zschunky/magicFlash64/pics/469-timing.png

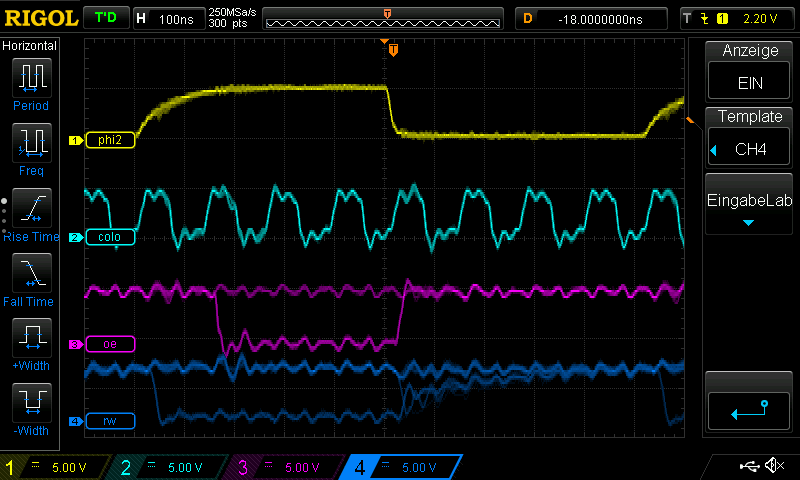
pics/469-timing.png
