zschunky/magicFlash64/pics/P_20190113_054123.jpg

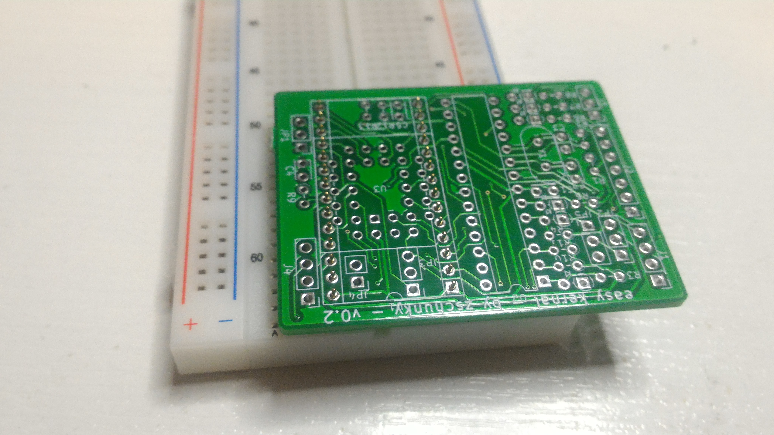
pics/P_20190113_054123.jpg
