zschunky/magicFlash64/pics/P_20190113_054204.jpg

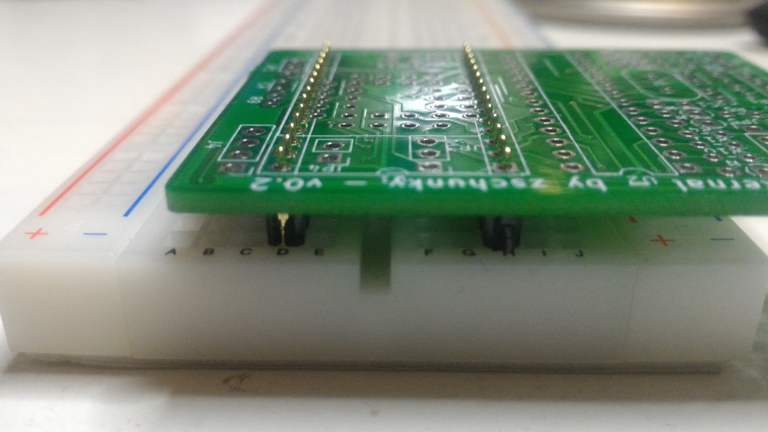
pics/P_20190113_054204.jpg
