zschunky/magicFlash64/pics/P_20190113_054526.jpg

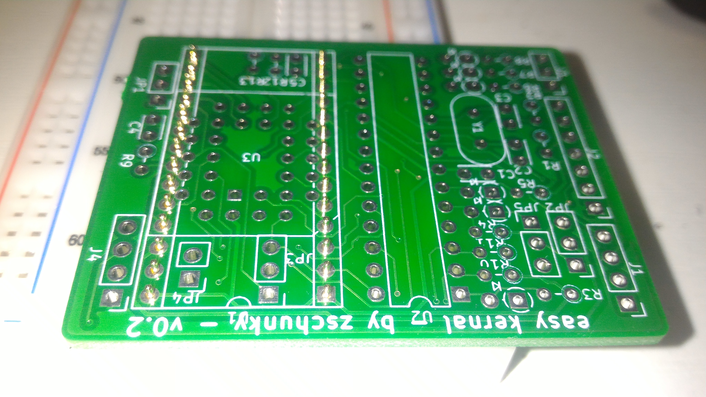
pics/P_20190113_054526.jpg
