zschunky/magicFlash64/pics/P_20190113_054540.jpg

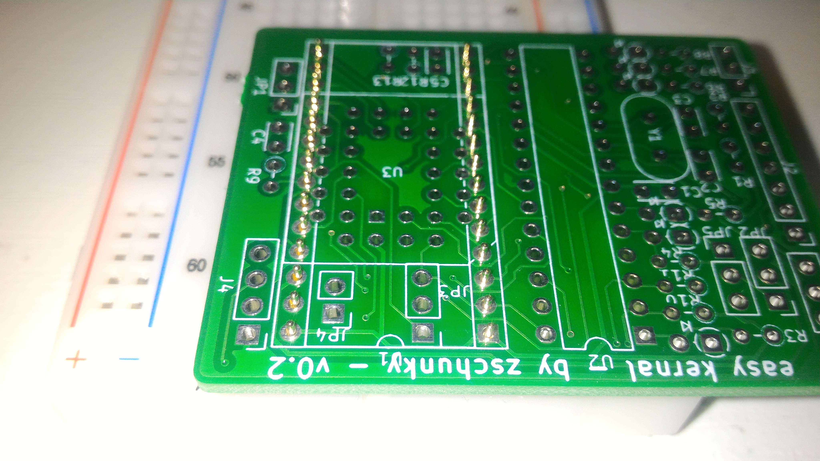
pics/P_20190113_054540.jpg
