zschunky/magicFlash64/pics/P_20190113_054853.jpg

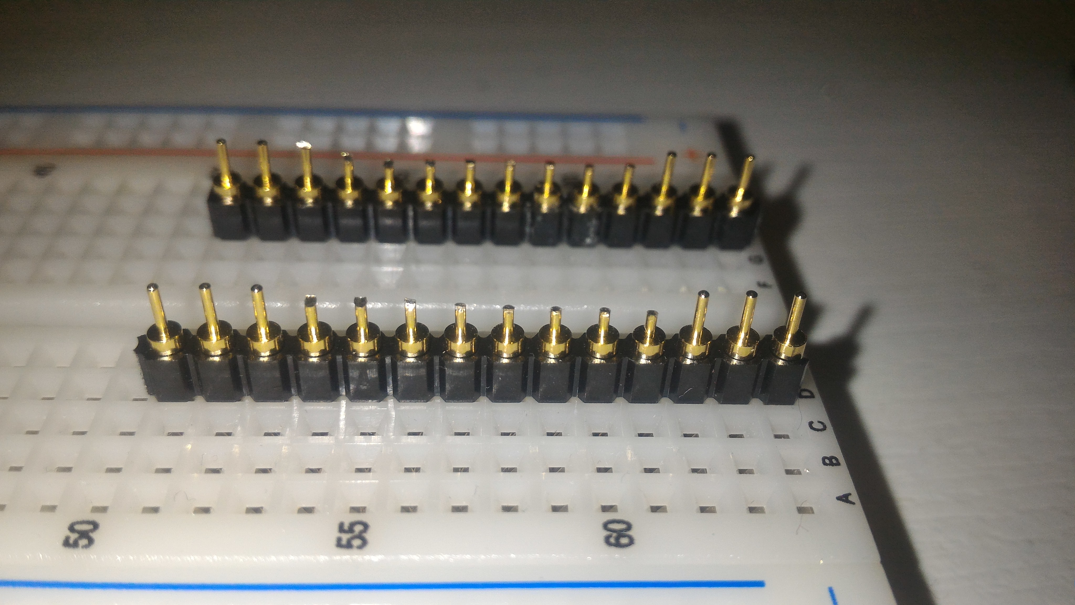
pics/P_20190113_054853.jpg
