zschunky/magicFlash64/pics/P_20190113_055543.jpg

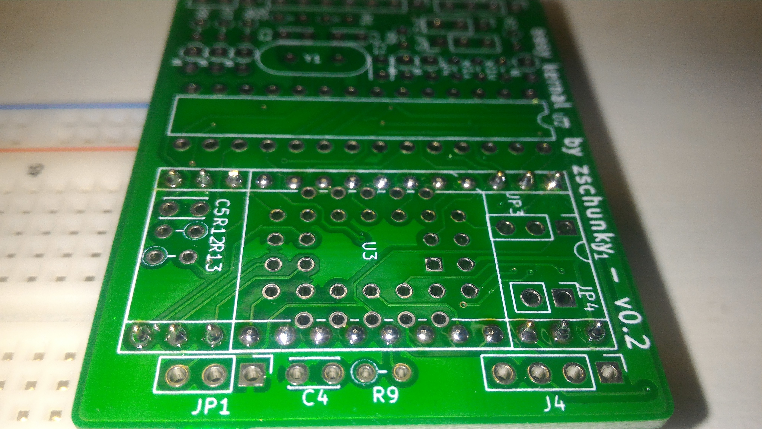
pics/P_20190113_055543.jpg
