zschunky/magicFlash64/pics/P_20190113_055739.jpg

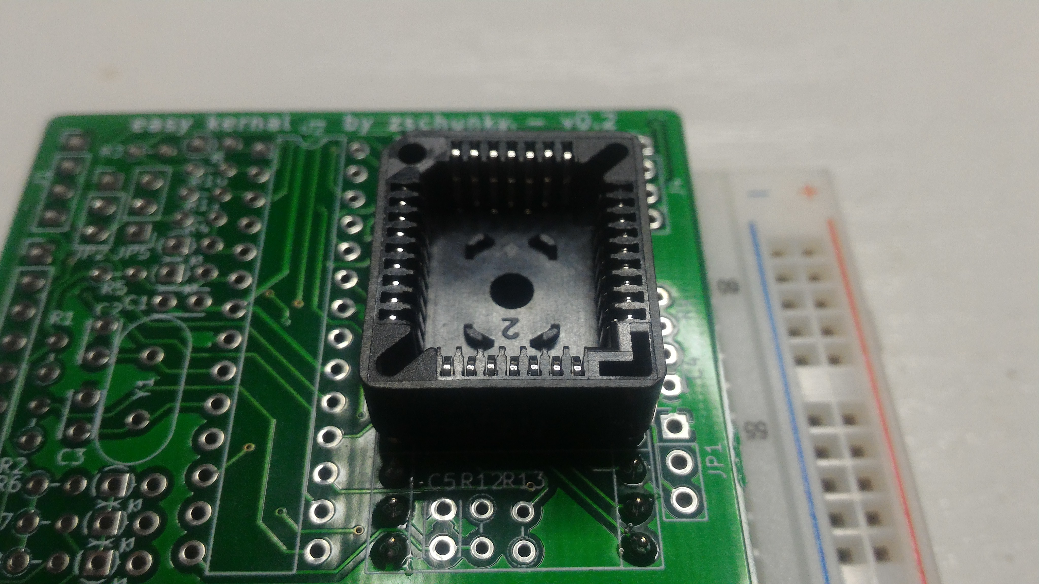
pics/P_20190113_055739.jpg
