zschunky/magicFlash64/pics/P_20190113_055753.jpg

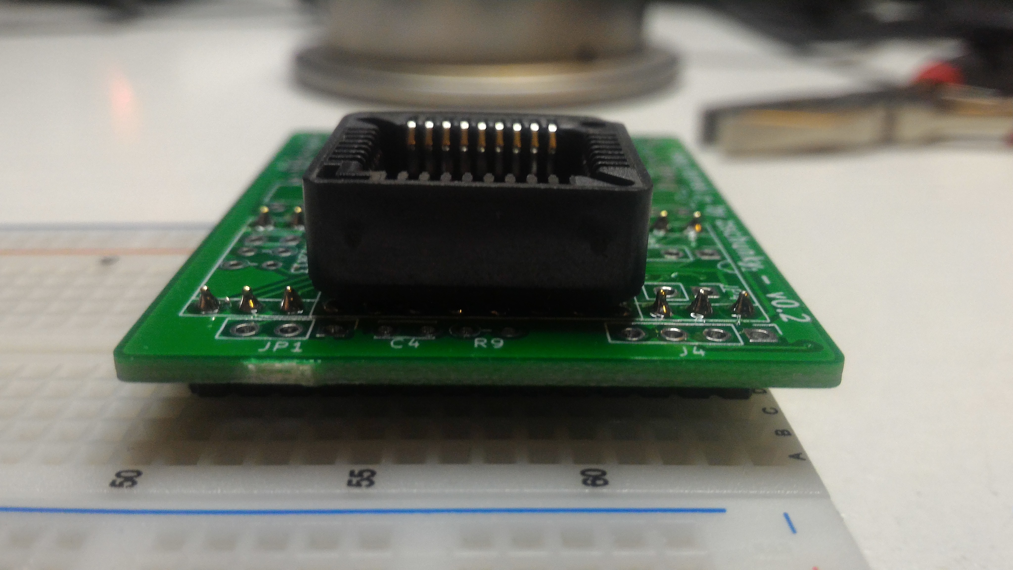
pics/P_20190113_055753.jpg
