zschunky/magicFlash64/pics/P_20190113_060007.jpg

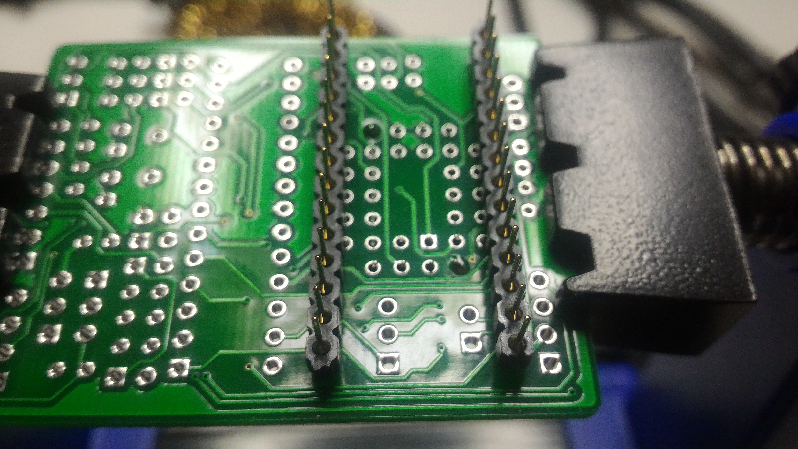
pics/P_20190113_060007.jpg
