zschunky/magicFlash64/pics/P_20190113_060031.jpg

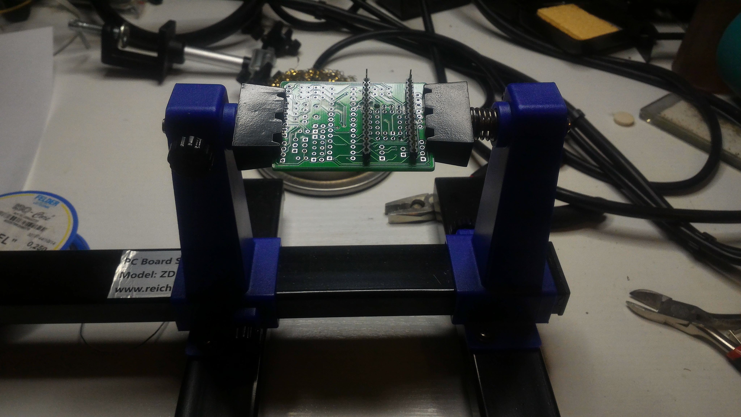
pics/P_20190113_060031.jpg
