zschunky/magicFlash64/pics/P_20190113_060040.jpg

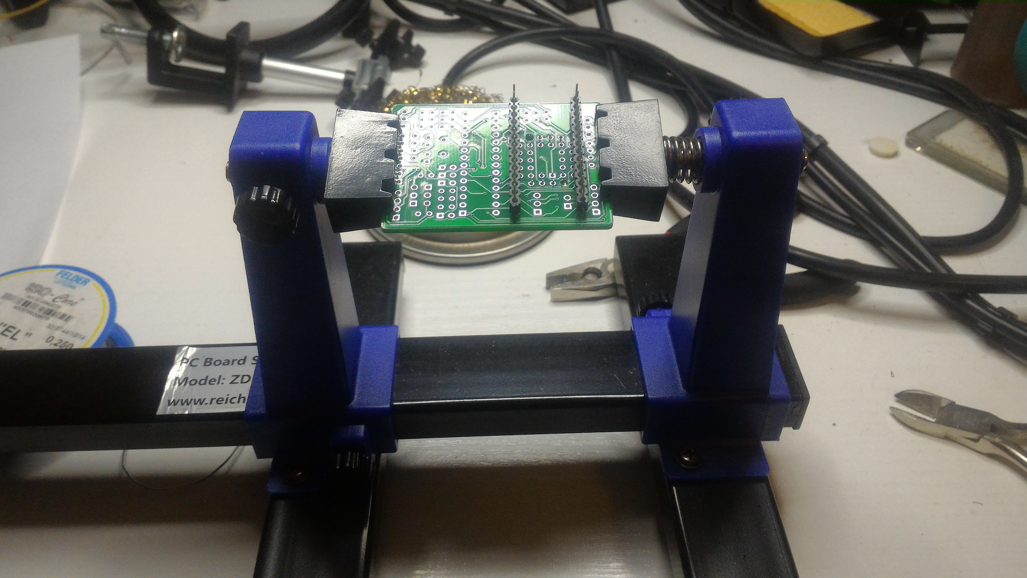
pics/P_20190113_060040.jpg
