zschunky/magicFlash64/pics/P_20190113_060500.jpg

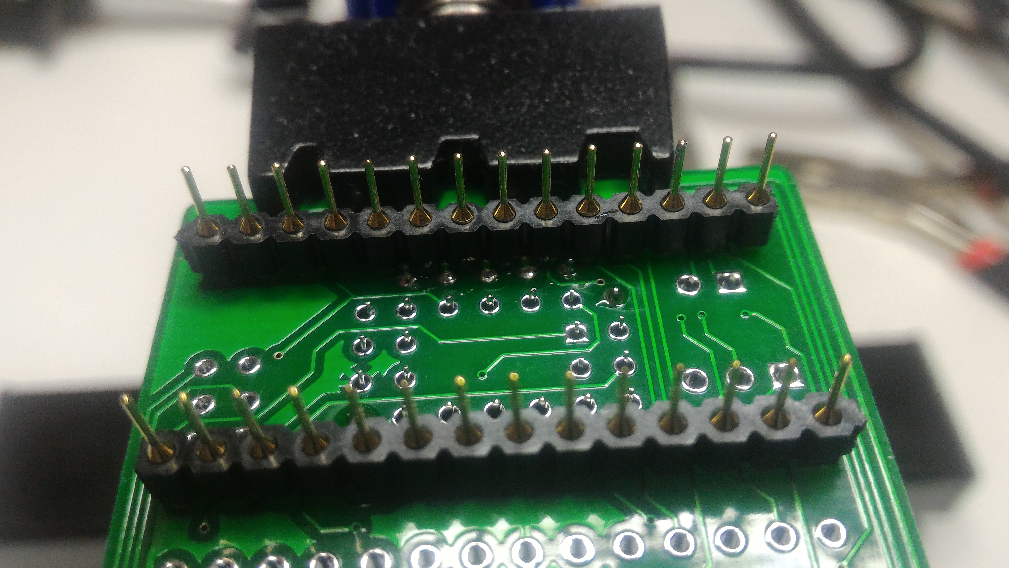
pics/P_20190113_060500.jpg
