zschunky/magicFlash64/pics/P_20190113_060512.jpg

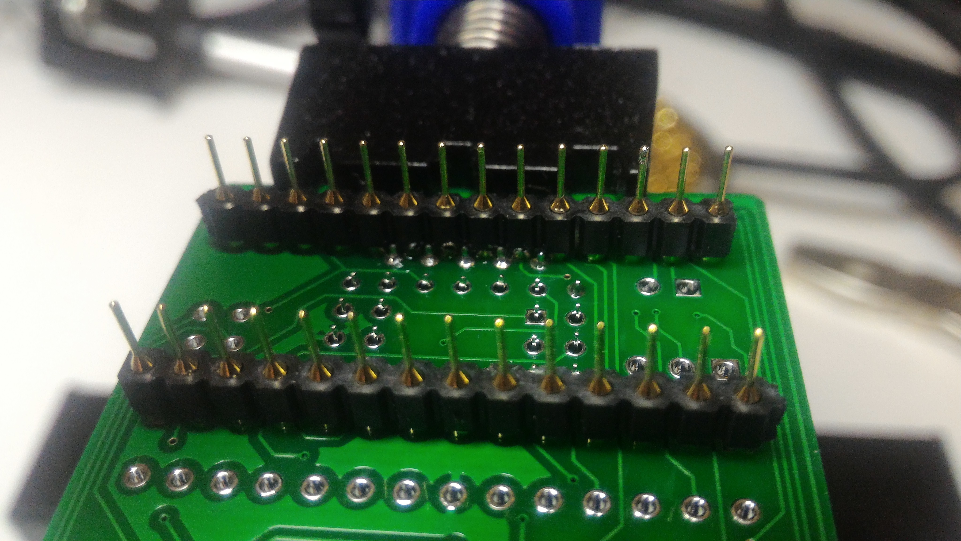
pics/P_20190113_060512.jpg
