zschunky/magicFlash64/pics/P_20190113_075411.jpg

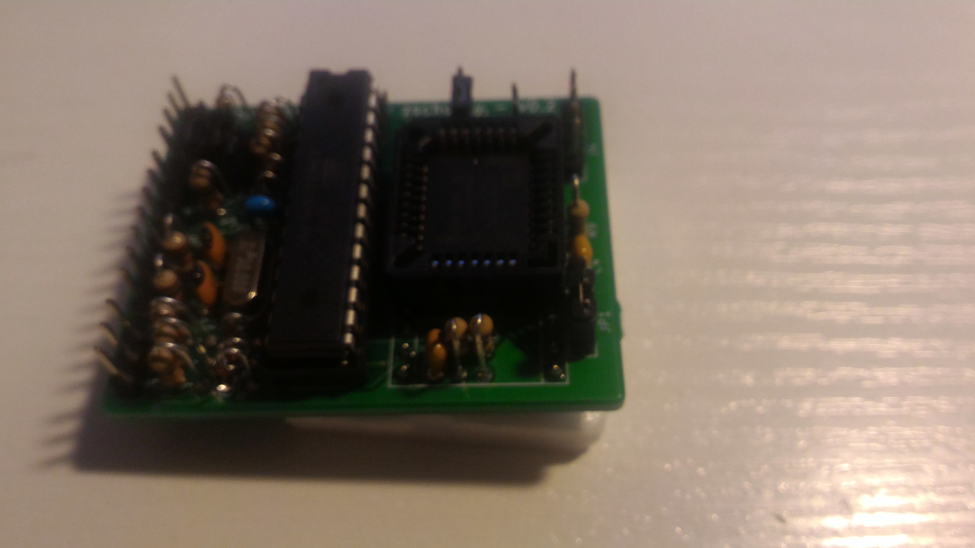
pics/P_20190113_075411.jpg
