zschunky/magicFlash64/pics/P_20190113_075420.jpg

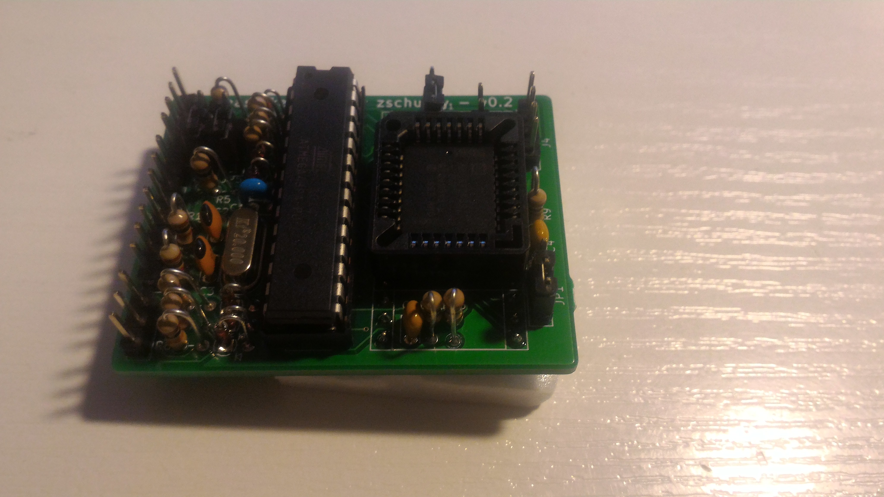
pics/P_20190113_075420.jpg
