zschunky/magicFlash64/pics/P_20190113_075424.jpg

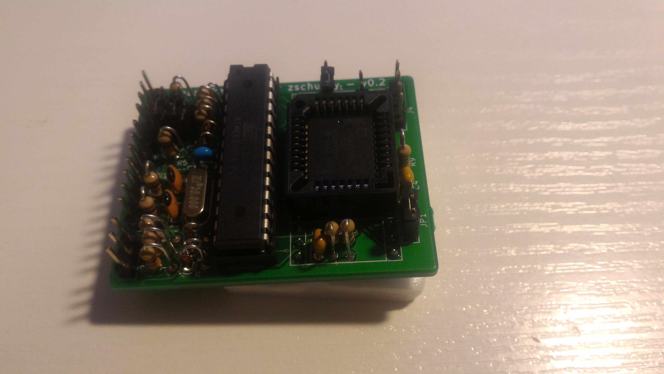
pics/P_20190113_075424.jpg
