zschunky/magicFlash64/pics/P_20190113_075440.jpg

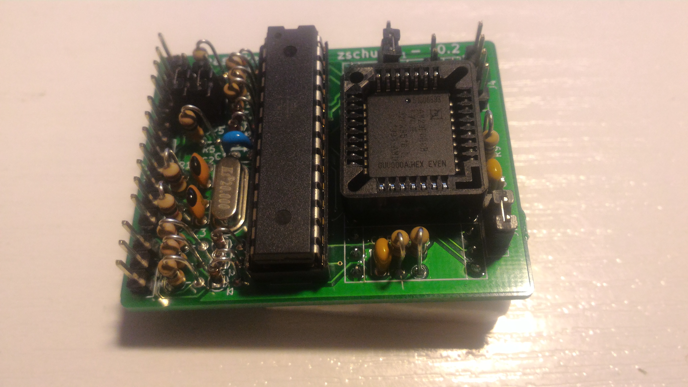
pics/P_20190113_075440.jpg
