zschunky/magicFlash64/pics/P_20190203_124354.jpg

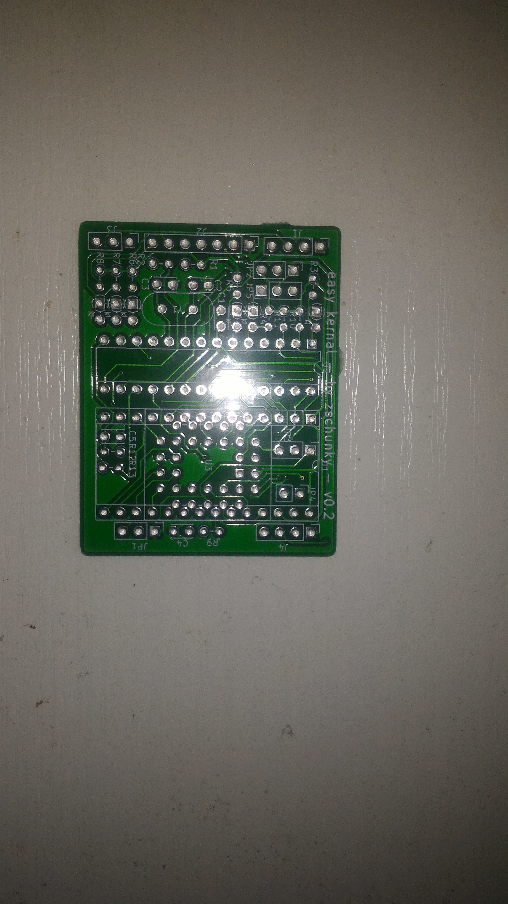
pics/P_20190203_124354.jpg
