zschunky/magicFlash64/pics/P_20190203_193504.jpg

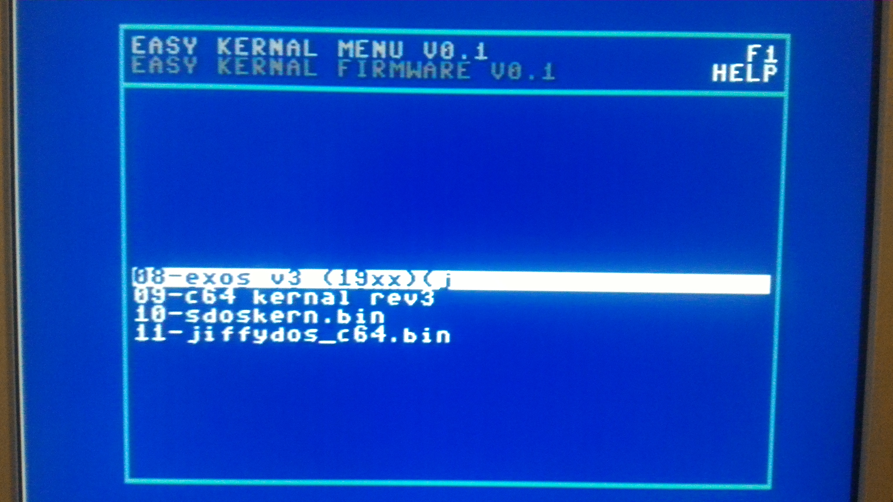
pics/P_20190203_193504.jpg
