zschunky/magicFlash64/pics/P_20190203_193543.jpg

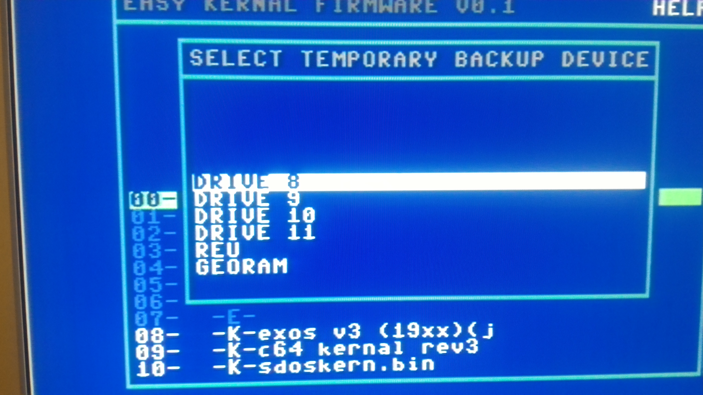
pics/P_20190203_193543.jpg
