zschunky/magicFlash64/pics/P_20190203_193612.jpg

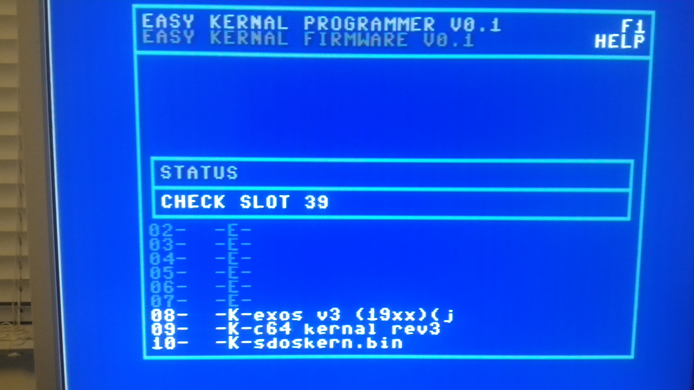
pics/P_20190203_193612.jpg
