zschunky/magicFlash64/pics/P_20190203_193618.jpg

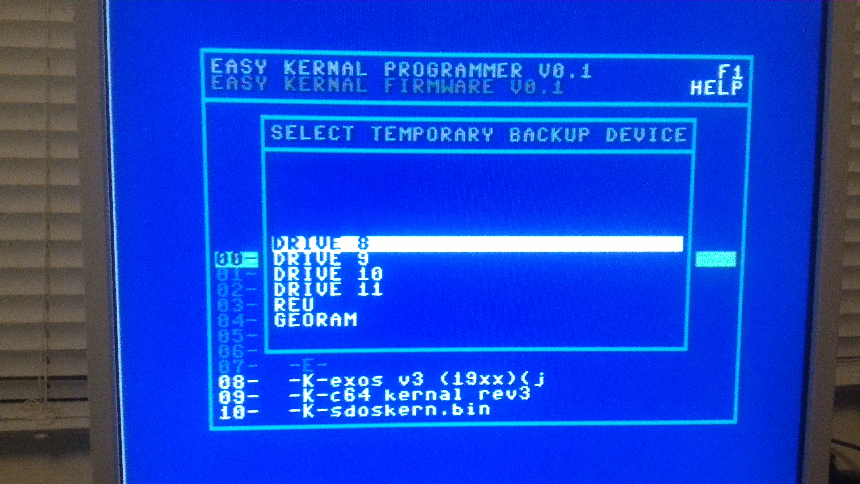
pics/P_20190203_193618.jpg
