zschunky/magicFlash64/pics/P_20190203_193620.jpg

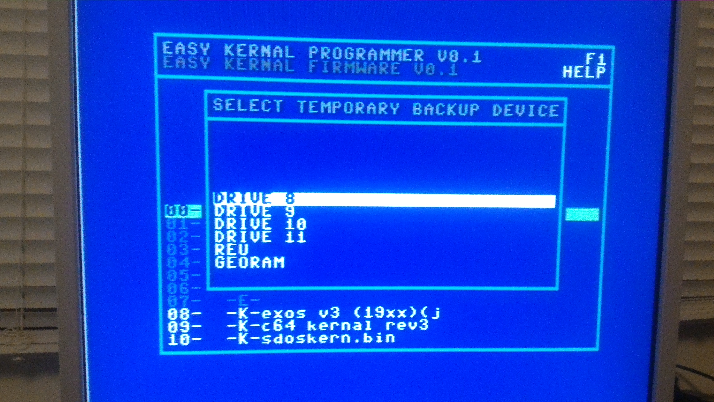
pics/P_20190203_193620.jpg
