zschunky/magicFlash64/pics/P_20190203_193637.jpg

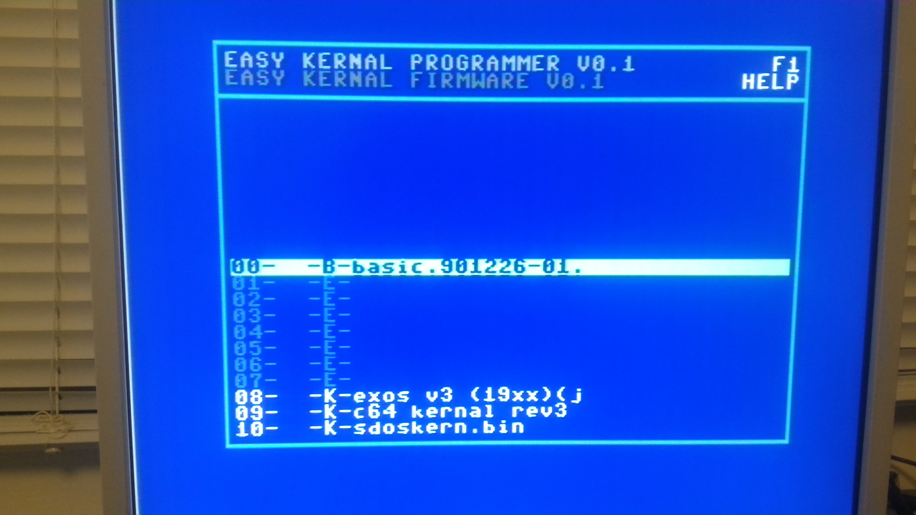
pics/P_20190203_193637.jpg
