zschunky/magicFlash64/pics/P_20190222_200331.jpg

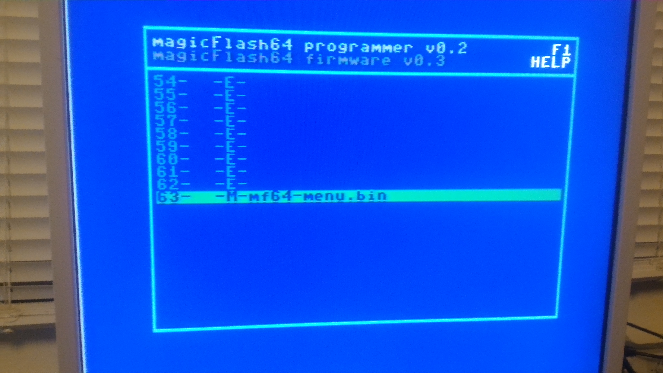
pics/P_20190222_200331.jpg
