zschunky/magicFlash64/pics/P_20190222_200403.jpg

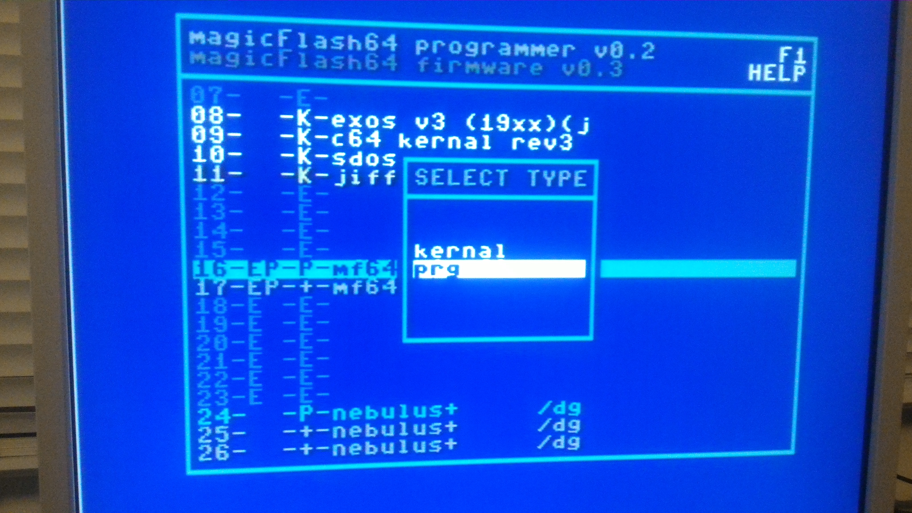
pics/P_20190222_200403.jpg
