zschunky/magicFlash64/pics/P_20190222_200522.jpg

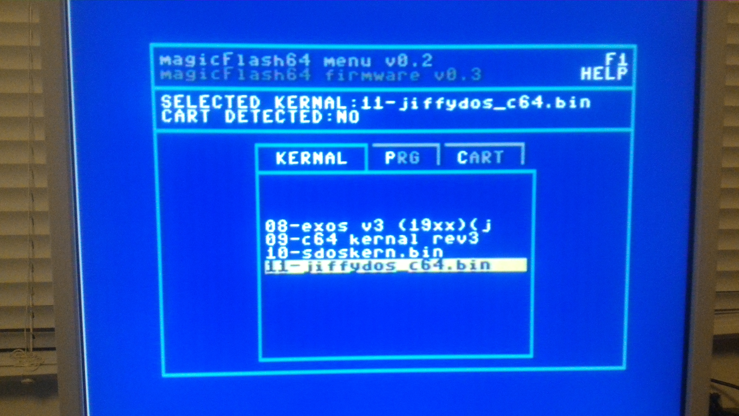
pics/P_20190222_200522.jpg
