zschunky/magicFlash64/pics/P_20190222_200538.jpg

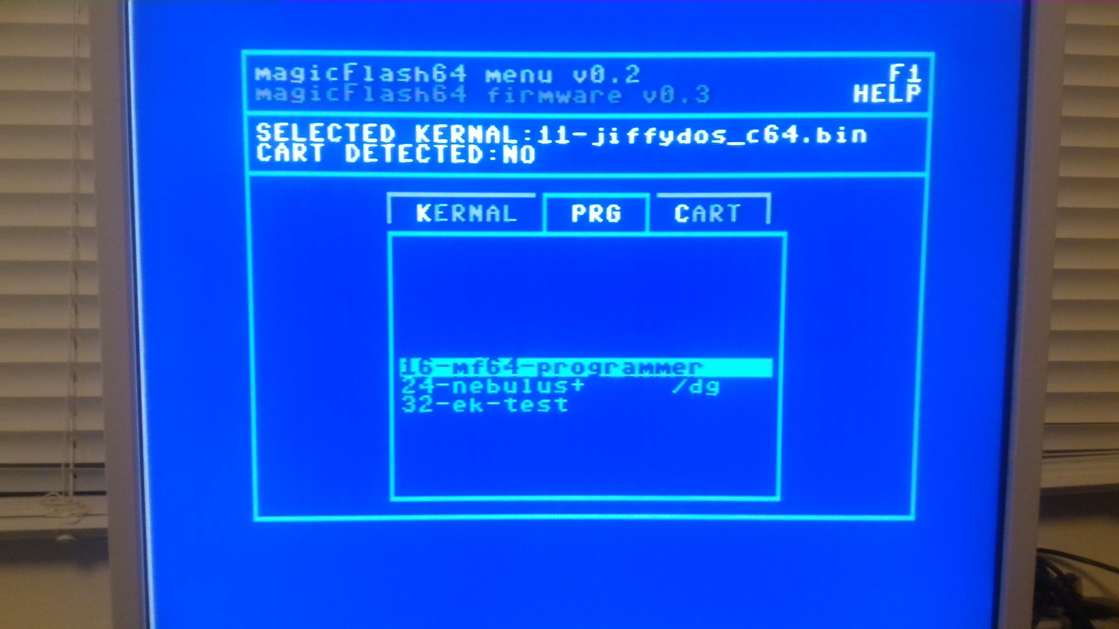
pics/P_20190222_200538.jpg
